avnguyen08/Monitoring_System/Hardware_Filter_SSS/Hardware_Filter_Cleaned_Up.asc

C1: cap; 0.1µF
C2: cap; 0.1µF
C3: cap; 0.1µF
C4: cap; 0.1µF
C7: cap; 0.1µF
C11: cap; .002µF
D1: diode; 1N914
R1: res; 30.1k
R2: res; 20k
R3: res; 110k
R4: res; 25.5k
R5: res; 187k
R6: res; 22k
R8: res; 22k
R9: res; 10k
R10: res; 1Meg
R11: res; 4.7k
R12: res; 10k
R13: res; 80.6k
R14: res; 80.6k
R15: res; 1.82k
R16: res; 10k
R17: res; 80.6k
R18: res; 80.6k
R19: res; 3.65k
R20: res; 4.7k
R22: res; 10k
R23: res; 1Meg
R24: res; 10k
R25: res; 16.2k
R26: res; 10k
R27: res; 10k
U1: UniversalOpAmp3
U2: UniversalOpAmp3
U3: UniversalOpAmp3
U4: UniversalOpAmp3
U5: UniversalOpAmp3
U7: potentiometer; Rtot=20K wiper=.5
U21: potentiometer; Rtot=20K wiper=.3675
V1: voltage; 5V
V2: voltage; -5V
V3: voltage; 0; AC 1
Named nets: 5V, 0, -5V, Input, E23, E60, T/P-1, T/P-2, 4x, 2x
.SUBCKT potentiometer 1 2 3
.param w=limit(wiper,1m,.999)
R0 1 3 {Rtot*(1-w)}
R1 3 2 {Rtot*(w)}
.ENDS
(AC Only)
.ac dec 1000 1 100
